pepelepoisson/CroqueLivresSaint2021/CAD/CNC/croque-livres_silouette.jpg

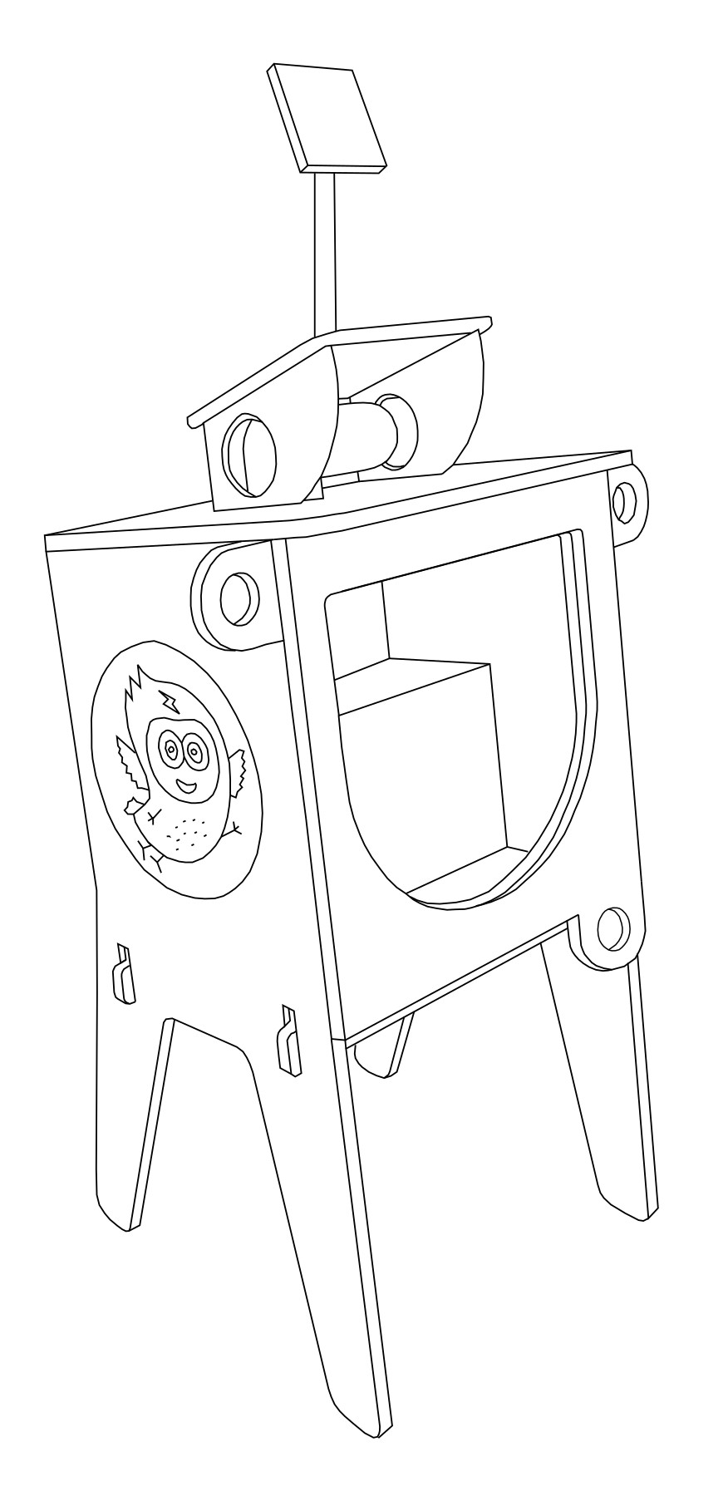
CAD/CNC/croque-livres_silouette.jpg
