pepelepoisson/CroqueLivresSaint2021/CAD/silhouette_1.png

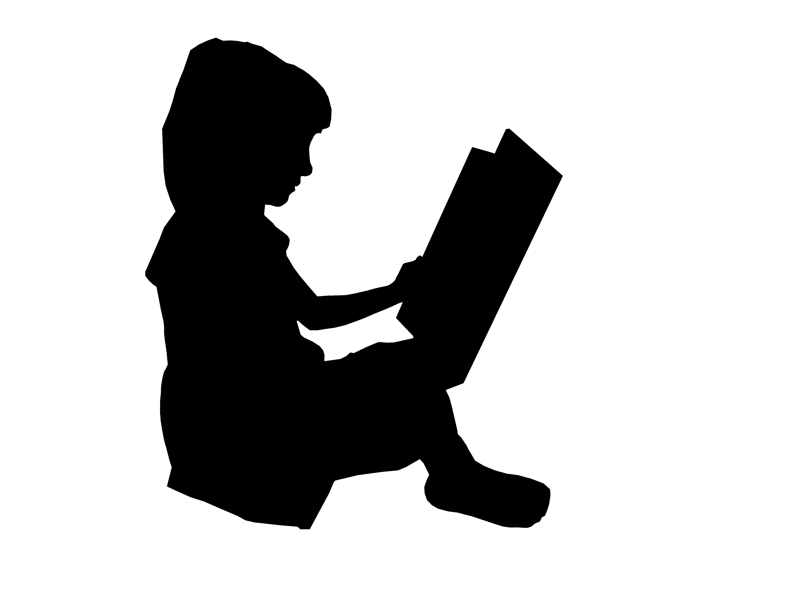
CAD/silhouette_1.png
