pepelepoisson/CroqueLivresSaint2021/CAD/silhouette_2.png

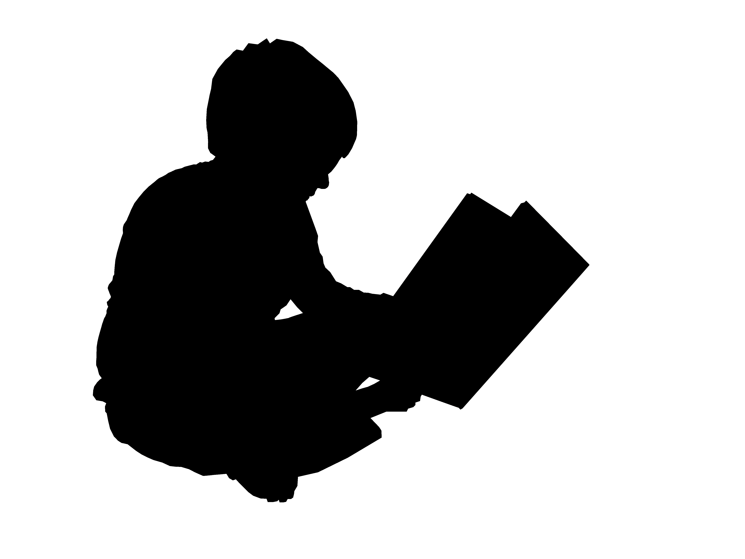
CAD/silhouette_2.png
