pepelepoisson/CroqueLivresSaint2021/CAD/silhouette_3.png

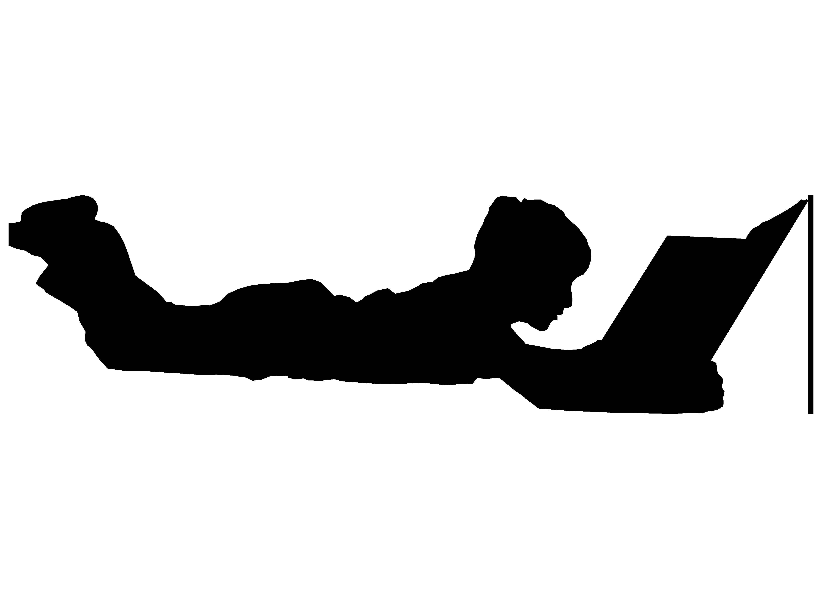
CAD/silhouette_3.png
