pepelepoisson/CroqueLivresSaint2021/CAD/silhouette_4.png

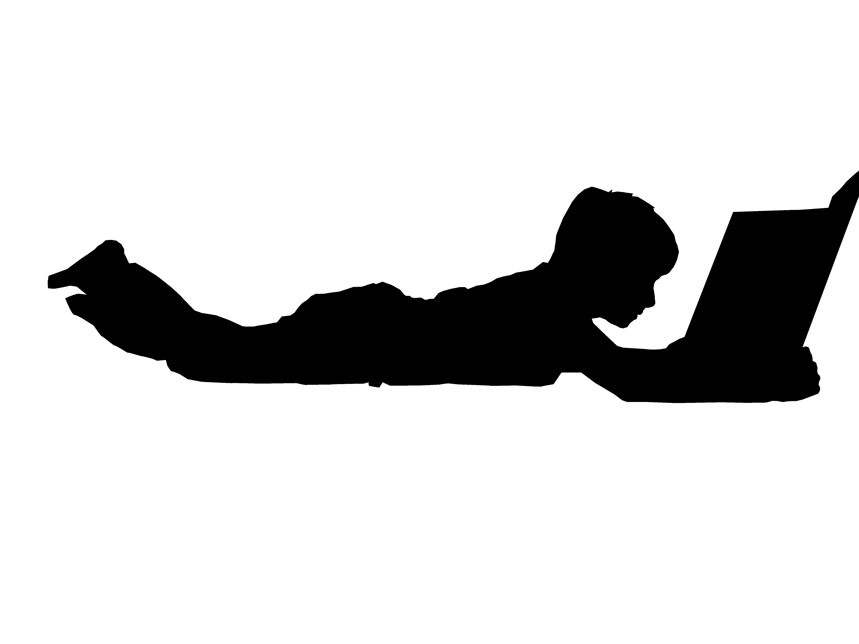
CAD/silhouette_4.png
