pepelepoisson/CroqueLivresSaint2021/Code/bitmaps/LesAventuriersDeSaint-Gérard.bmp

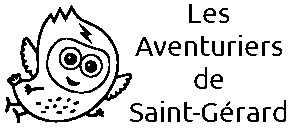
Code/bitmaps/LesAventuriersDeSaint-Gérard.bmp
