pepelepoisson/CroqueLivresSaint2021/Code/bitmaps/LesAventuriersDeSaint-Gérard.png

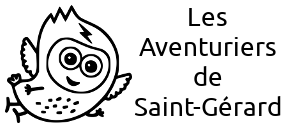
Code/bitmaps/LesAventuriersDeSaint-Gérard.png
