pepelepoisson/CroqueLivresSaint2021/Code/bitmaps/LesAventuriersDeSaint-Gérard_mirror_vertical.bmp

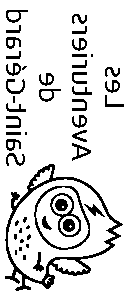
Code/bitmaps/LesAventuriersDeSaint-Gérard_mirror_vertical.bmp
