pepelepoisson/CroqueLivresSaint2021/Code/bitmaps/LesAventuriersDeSaint-Gérard_mirror_vertical_negatif.bmp

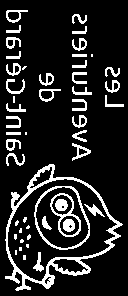
Code/bitmaps/LesAventuriersDeSaint-Gérard_mirror_vertical_negatif.bmp
