pepelepoisson/CroqueLivresSaint2021/Code/bitmaps/LesAventuriersDeSaint-GérardNegatif2.bmp

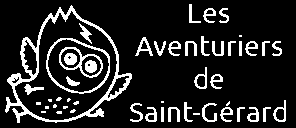
Code/bitmaps/LesAventuriersDeSaint-GérardNegatif2.bmp
