pepelepoisson/CroqueLivresSaint2021/Code/bitmaps/LesAventuriersDeSaint-GérardNegatifVertical.bmp

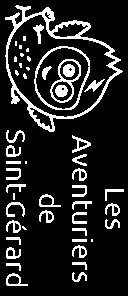
Code/bitmaps/LesAventuriersDeSaint-GérardNegatifVertical.bmp
