pepelepoisson/CroqueLivresSaint2021/Code/bitmaps/PapasInventeursEtJeunes.bmp

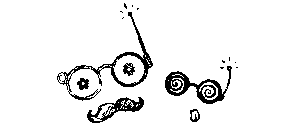
Code/bitmaps/PapasInventeursEtJeunes.bmp
