pepelepoisson/CroqueLivresSaint2021/Code/bitmaps/PapasInventeursEtJeunes_negatif_symetrique_vertical.bmp

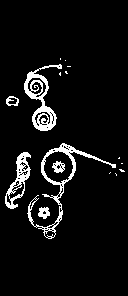
Code/bitmaps/PapasInventeursEtJeunes_negatif_symetrique_vertical.bmp
