pepelepoisson/CroqueLivresSaint2021/miniature.JPG

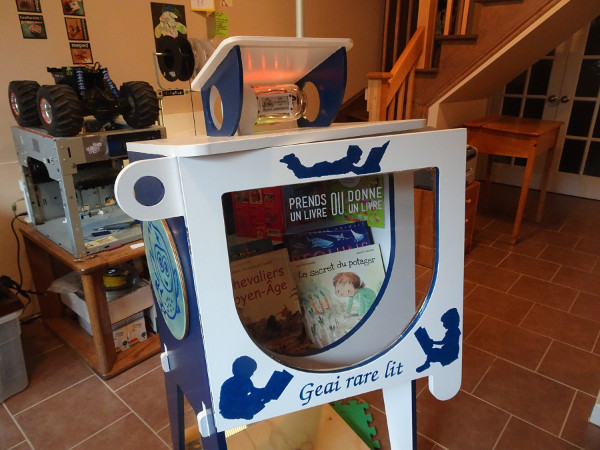
miniature.JPG
