pepelepoisson/CroqueLivresSaint2021/CAD/support_panneau_solaire_haut_V1.stl

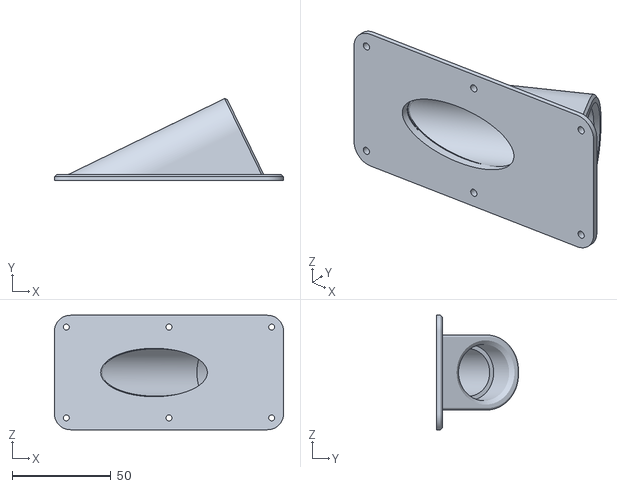
[picture p37: CAD file, 2021-05-12]
CAD/support_panneau_solaire_haut_V1.stl
116.0 x 41.5 x 58.0
