pepelepoisson/CroqueLivresSaint2021/CAD/CrocSaintGerard_V3-fixation_enceinte_verre_V1.stl

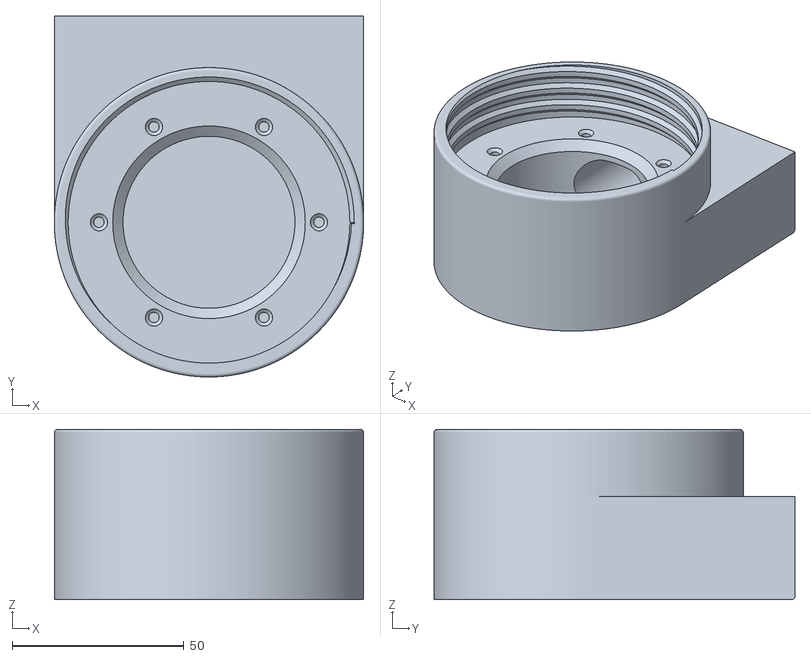
[picture p38: CAD file, 2021-05-12]
CAD/CrocSaintGerard_V3-fixation_enceinte_verre_V1.stl
90.0 x 105.0 x 49.5
