pepelepoisson/CroqueLivresSaint2021/CAD/support_panneau_solaire_haut_Contour_V1.stl

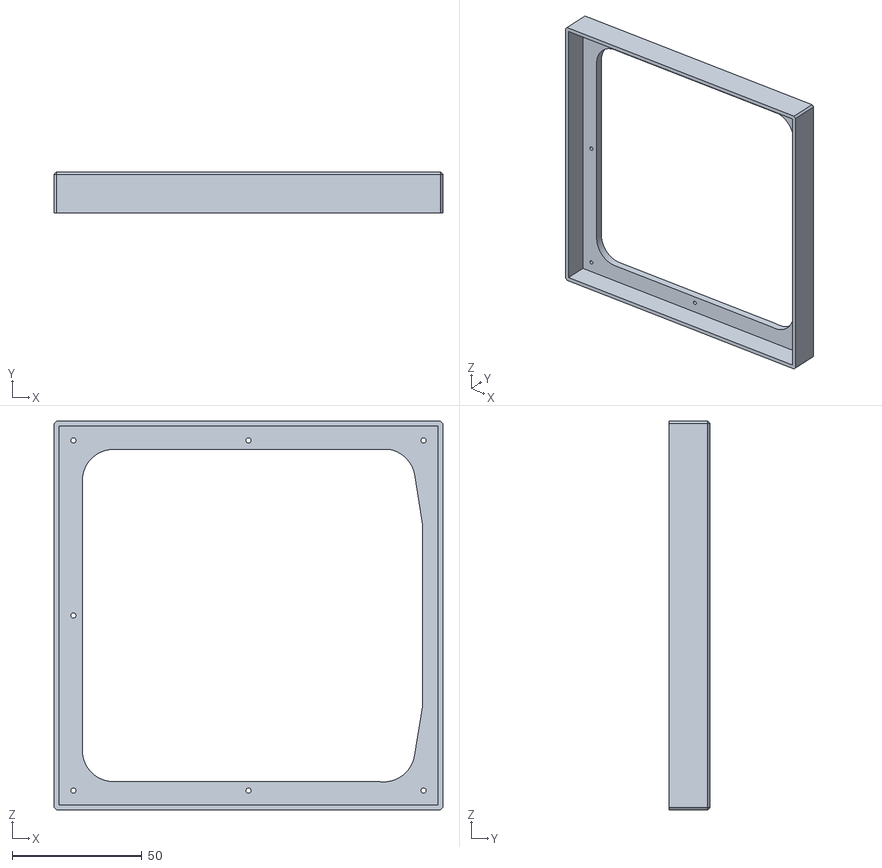
[picture p39: CAD file, 2021-05-12]
CAD/support_panneau_solaire_haut_Contour_V1.stl
150.0 x 16.0 x 150.0
