pepelepoisson/CroqueLivresSaint2021/CAD/Vis.FCStd

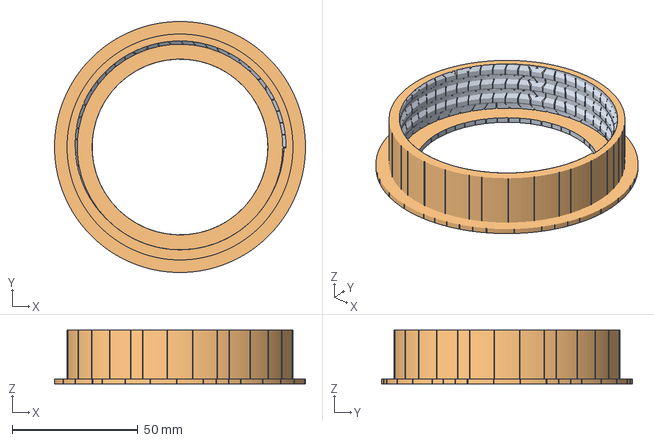
[picture p40: CAD file, 2021-05-12]
CAD/Vis.FCStd
100.0 x 100.0 x 21.5 mm
Body (Meshed)
