pepelepoisson/CroqueLivresSaint2021/CAD/CrocSaintGerard_V5-attache_leds_V1.stl

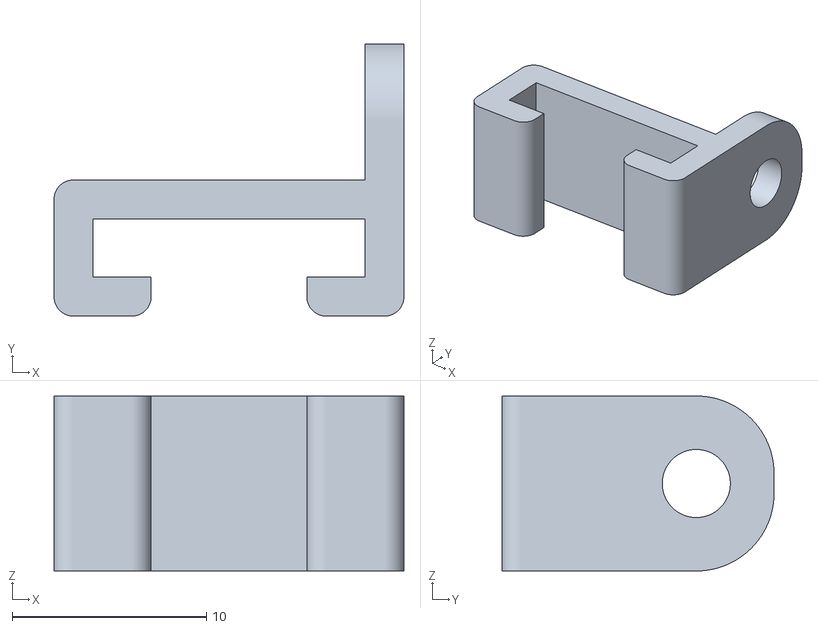
[picture p41: CAD file, 2021-05-12]
CAD/CrocSaintGerard_V5-attache_leds_V1.stl
18.0 x 14.0 x 9.00
